aerocat24/aerocat-v2/images/aerocat_with_uav_3.jpg

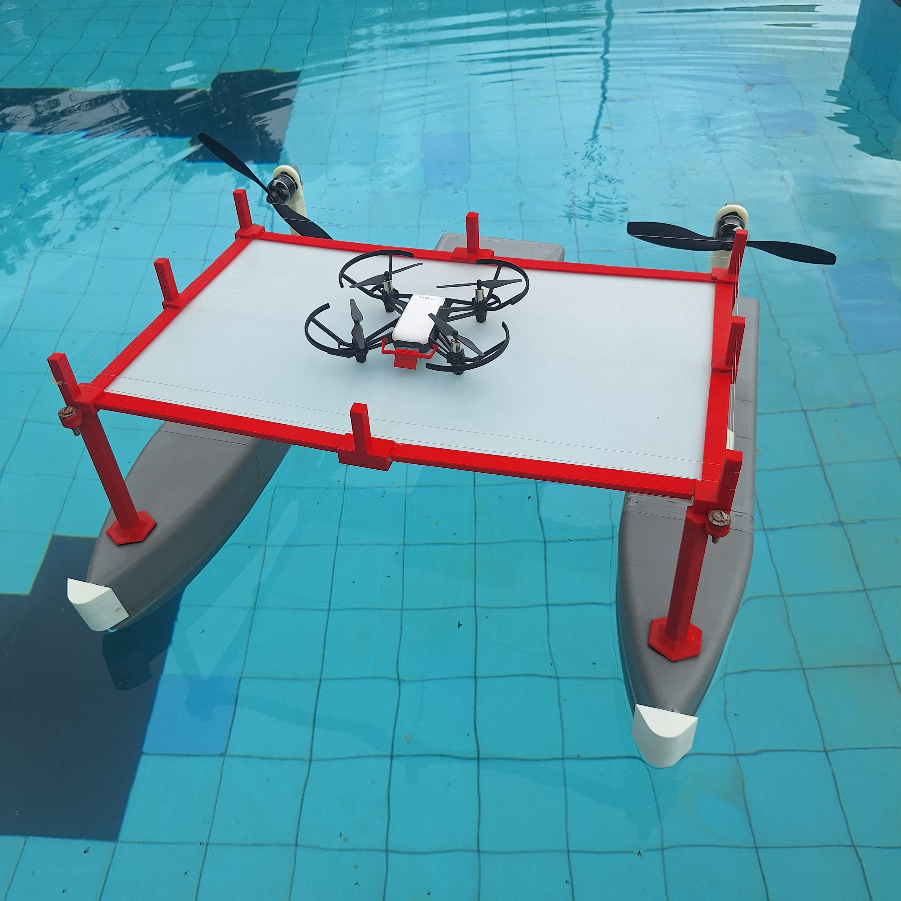
images/aerocat_with_uav_3.jpg
