aerocat24/aerocat-v2/images/aerocat_without_platform_1.jpg

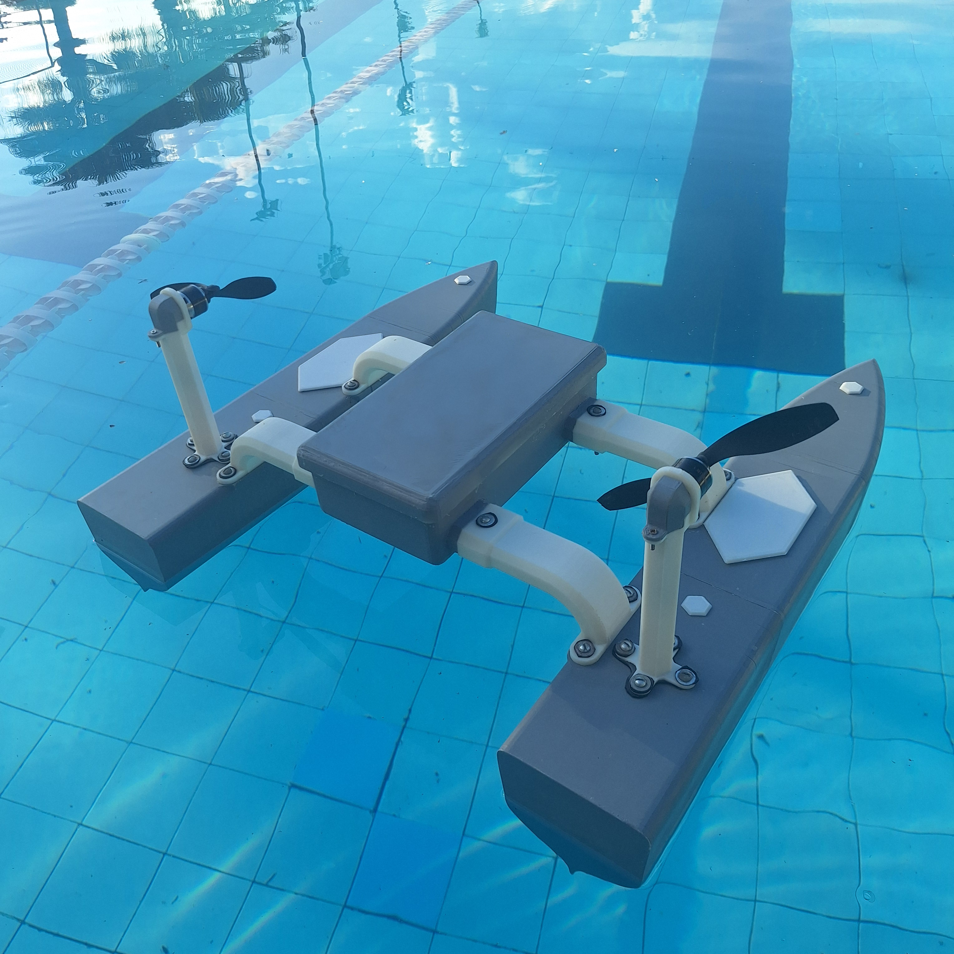
images/aerocat_without_platform_1.jpg
