aerocat24/aerocat-v2/images/aerocat_without_platform_4.jpg

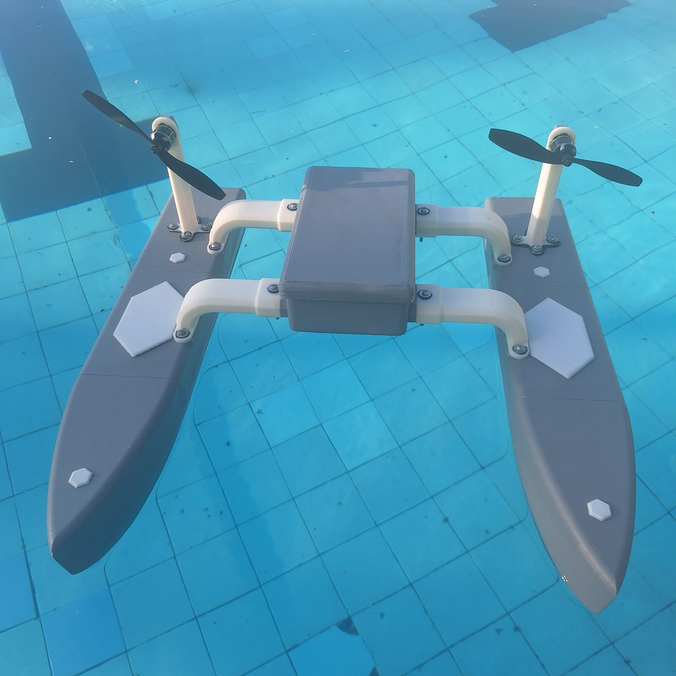
images/aerocat_without_platform_4.jpg
