aerocat24/aerocat-v2/images/mirror_suport.jpg

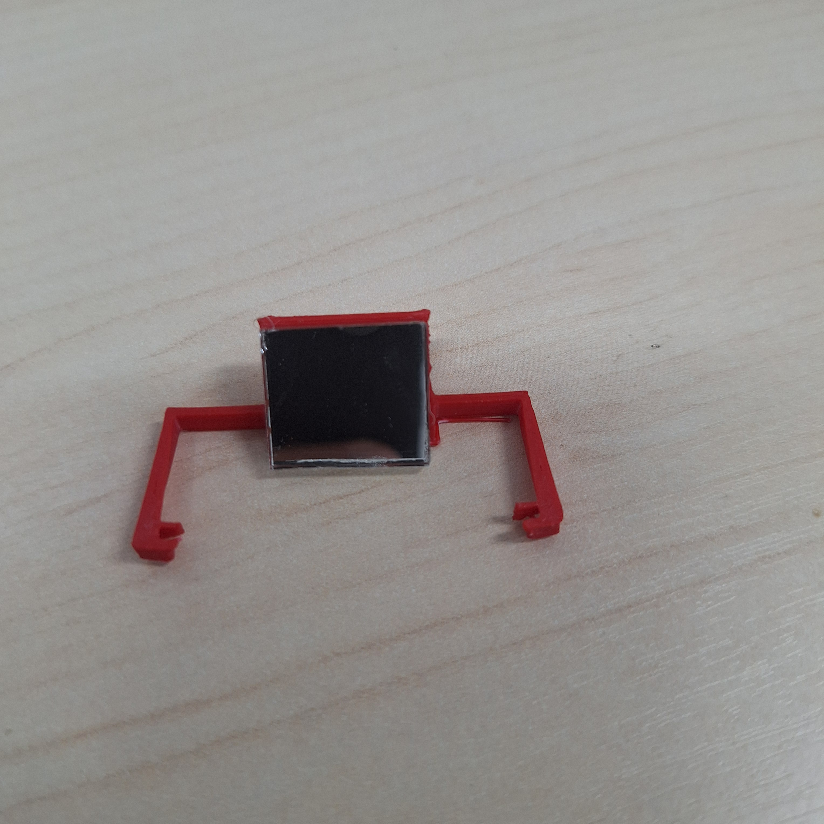
images/mirror_suport.jpg
