aerocat24/aerocat-v2/images/pcb_1.jpg

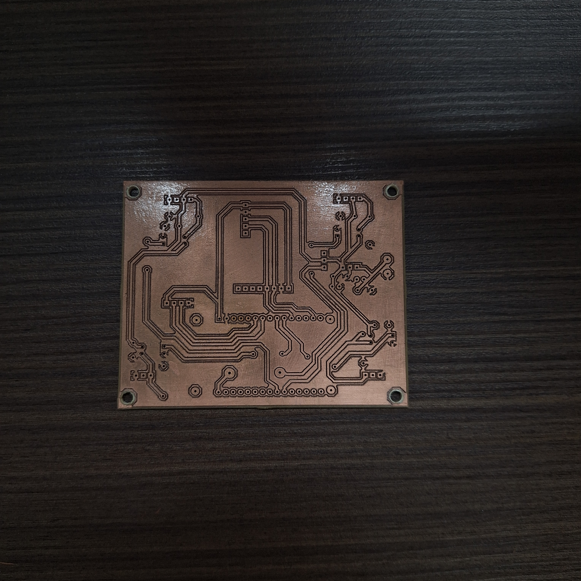
images/pcb_1.jpg
