aerocat24/aerocat-v2/images/uav_dji_tello_1.jpg

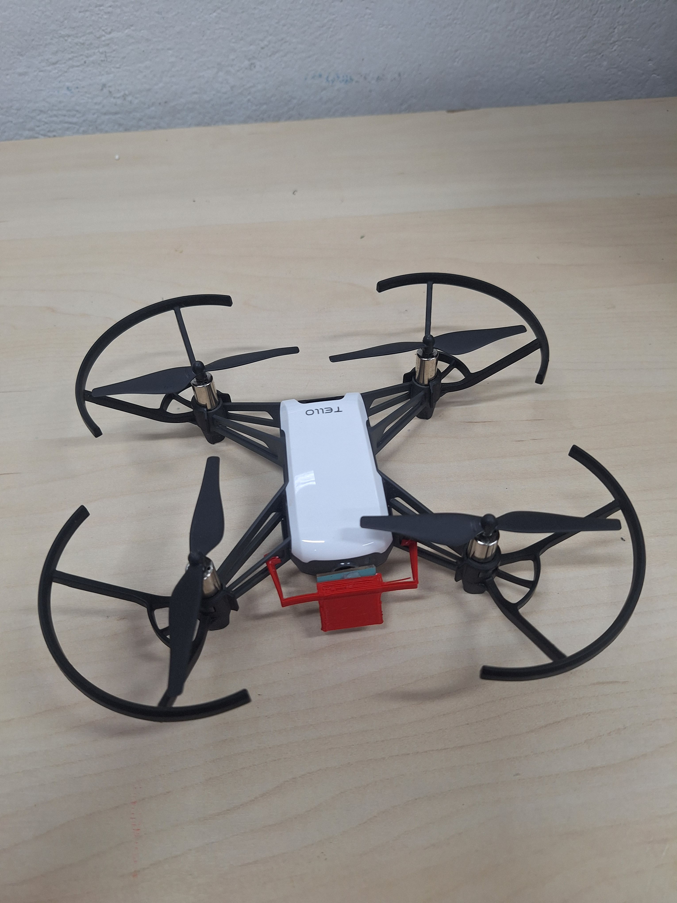
images/uav_dji_tello_1.jpg
