aerocat24/aerocat-v2/images/uav_dji_tello_2.jpg

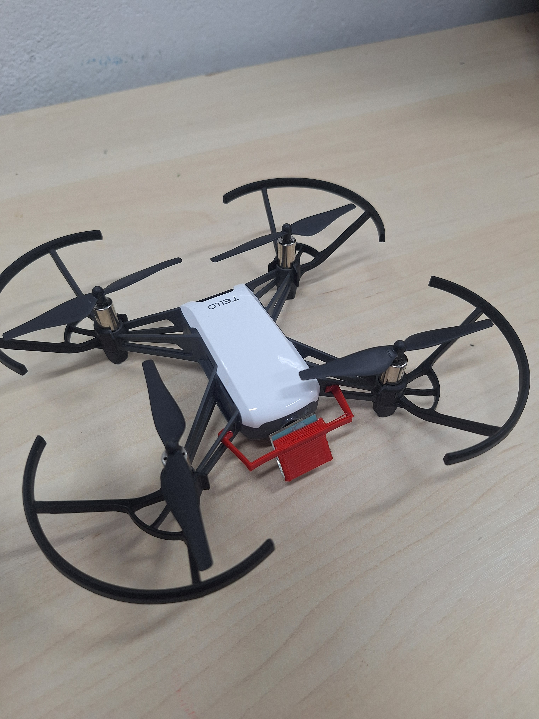
images/uav_dji_tello_2.jpg
