aerocat24/aerocat-v2/PCB/images/pcb_model.png

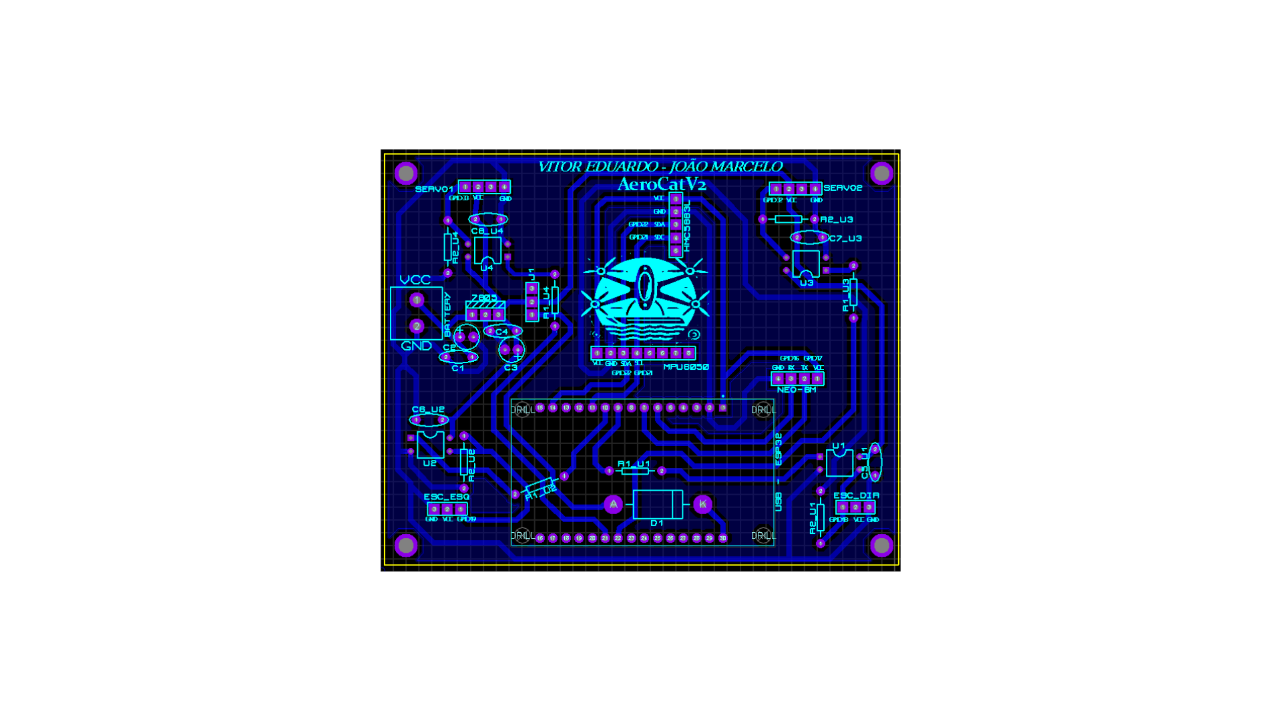
PCB/images/pcb_model.png
