aerocat24/aerocat-v2/PCB/images/Routes.jpg

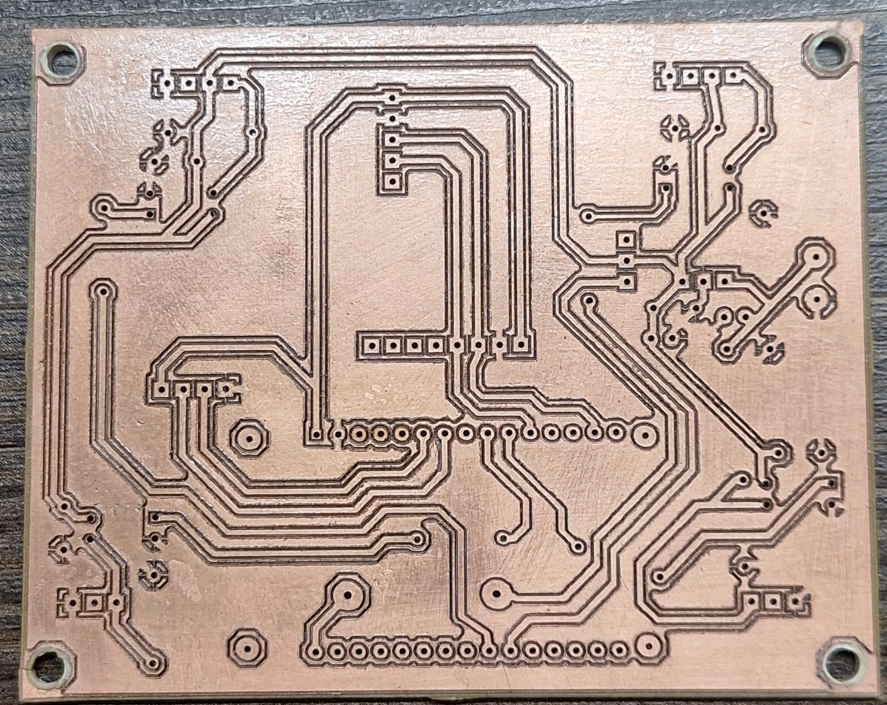
PCB/images/Routes.jpg
