aerocat24/aerocat-v2/STL/images/01_front_hull.png

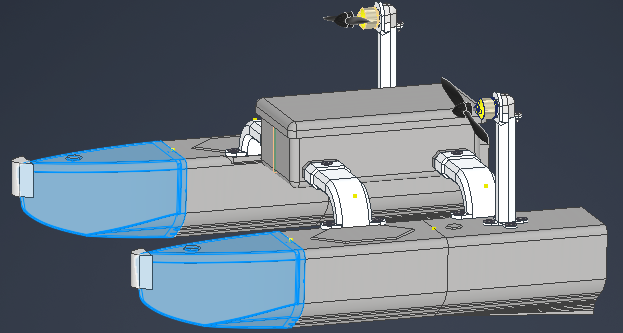
STL/images/01_front_hull.png
