aerocat24/aerocat-v2/STL/images/02_right_middle_hull.png

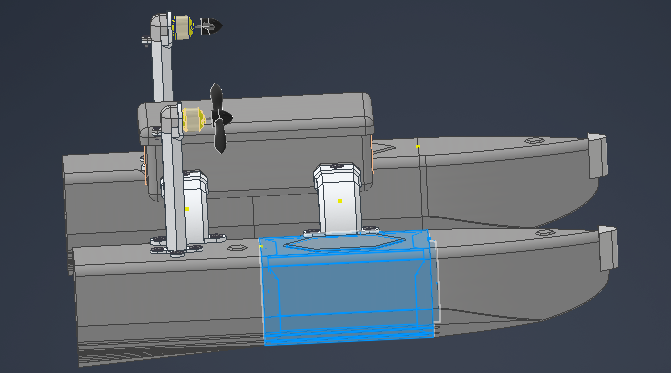
STL/images/02_right_middle_hull.png
