aerocat24/aerocat-v2/STL/images/03_left_middle_hull.png

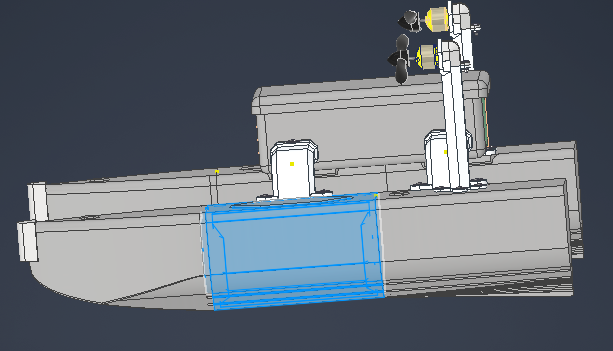
STL/images/03_left_middle_hull.png
