aerocat24/aerocat-v2/STL/images/04_right_rear_hull.png

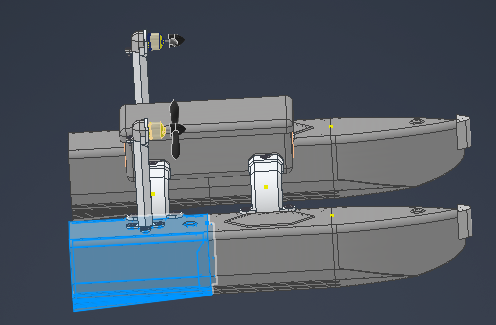
STL/images/04_right_rear_hull.png
