aerocat24/aerocat-v2/STL/images/05_left_rear_hull.png

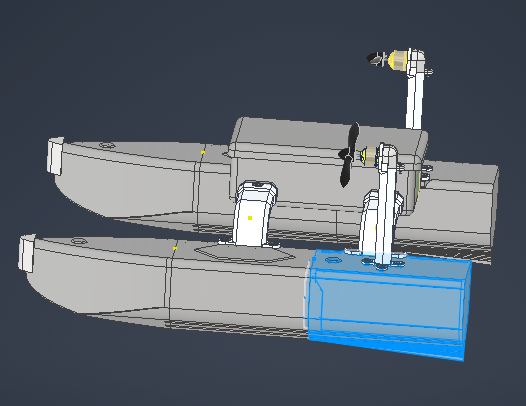
STL/images/05_left_rear_hull.png
