aerocat24/aerocat-v2/STL/images/06_small_hull_cover.png

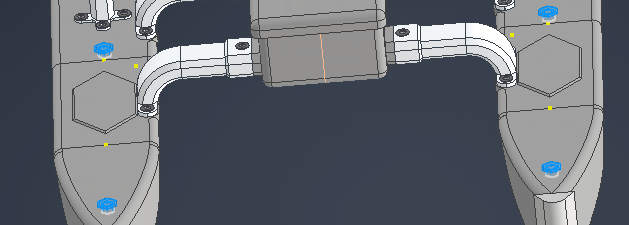
STL/images/06_small_hull_cover.png
