aerocat24/aerocat-v2/STL/images/07_large_hull_cover.png

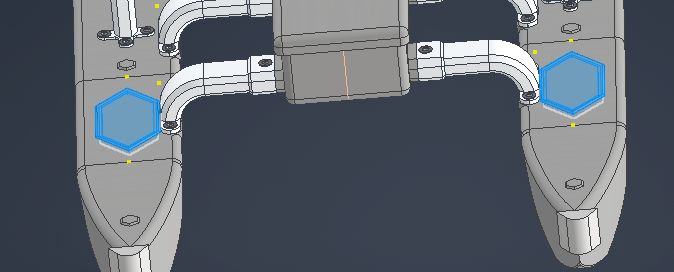
STL/images/07_large_hull_cover.png
