aerocat24/aerocat-v2/STL/images/08_module_hull_handle.png

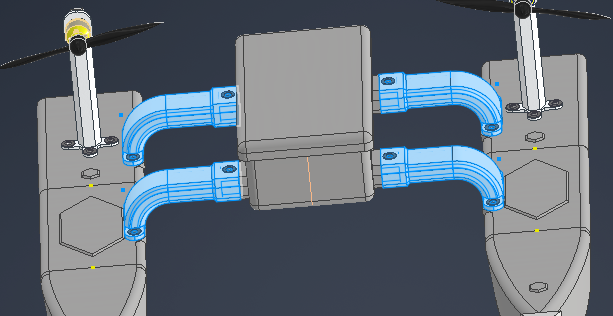
STL/images/08_module_hull_handle.png
