aerocat24/aerocat-v2/STL/images/09_motor_base.png

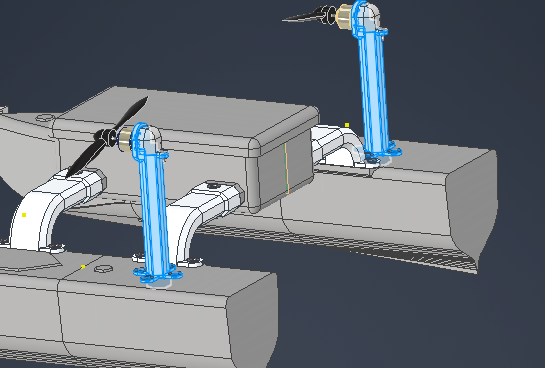
STL/images/09_motor_base.png
