aerocat24/aerocat-v2/STL/images/10_motor_base_cover.png

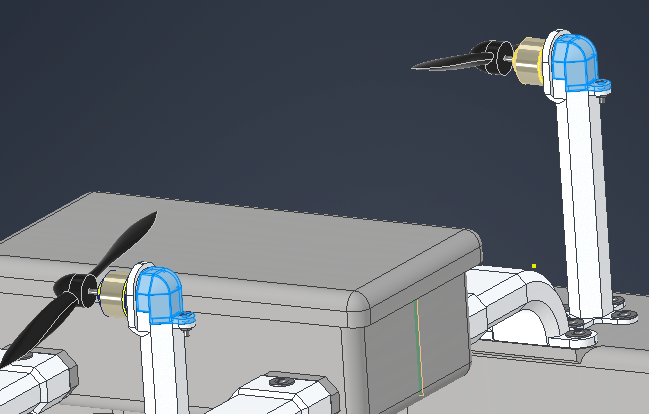
STL/images/10_motor_base_cover.png
