aerocat24/aerocat-v2/STL/images/11_module.png

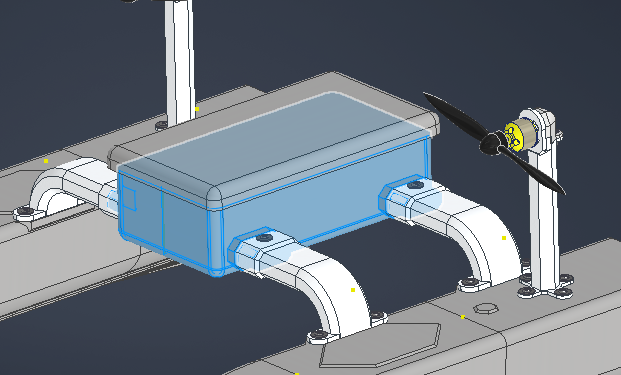
STL/images/11_module.png
