aerocat24/aerocat-v2/STL/images/12_module_cover.png

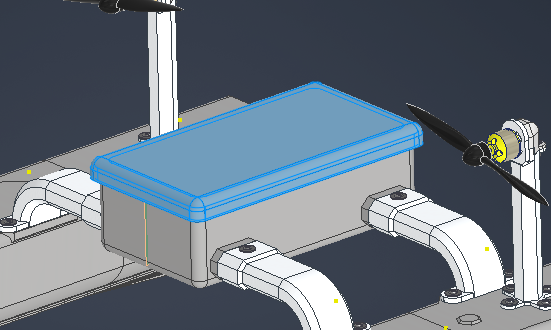
STL/images/12_module_cover.png
