aerocat24/aerocat-v2/STL/images/13_front_hull_guard.png

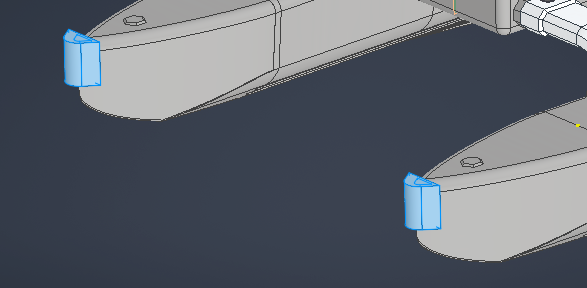
STL/images/13_front_hull_guard.png
