aerocat24/aerocat-v2/STL/images/14_front_platform_base.png

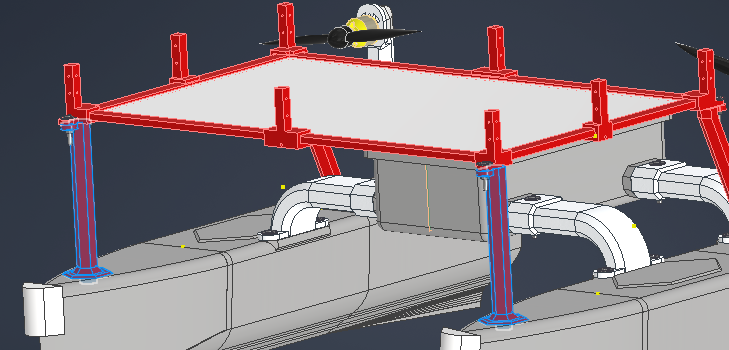
STL/images/14_front_platform_base.png
