aerocat24/aerocat-v2/STL/images/15_rear_platform_base.png

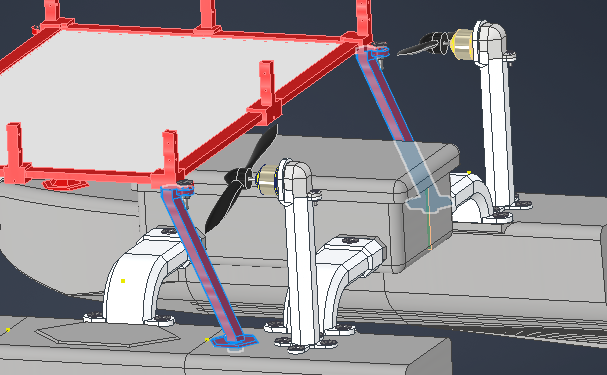
STL/images/15_rear_platform_base.png
