aerocat24/aerocat-v2/STL/images/16_large_platform_channel.png

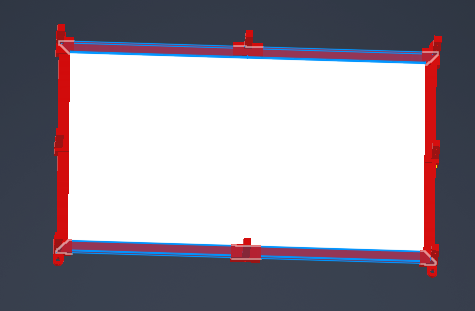
STL/images/16_large_platform_channel.png
