aerocat24/aerocat-v2/STL/images/17_small_platform_channel.png

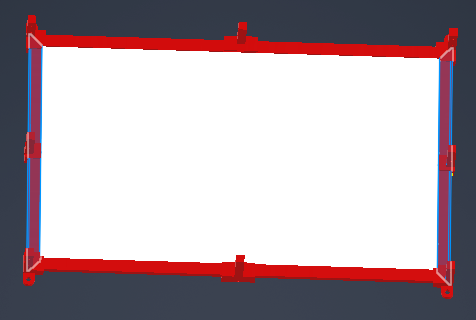
STL/images/17_small_platform_channel.png
