aerocat24/aerocat-v2/STL/images/19_platform_base_diagonal_channel_support_1.png

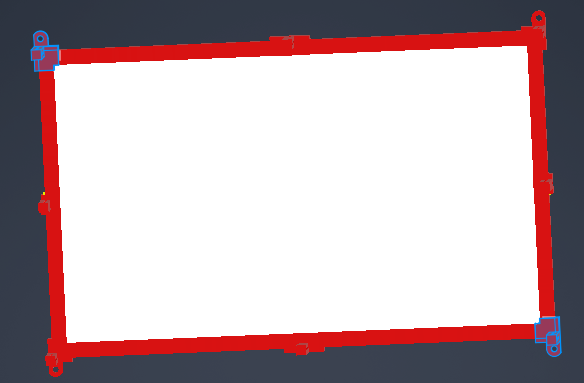
STL/images/19_platform_base_diagonal_channel_support_1.png
