aerocat24/aerocat-v2/STL/images/20_platform_base_diagonal_channel_support_2.png

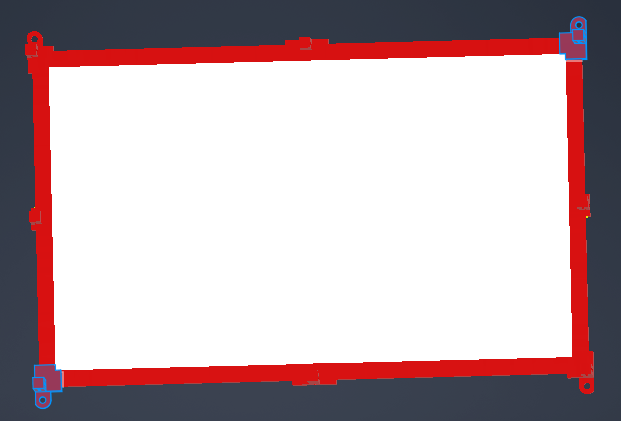
STL/images/20_platform_base_diagonal_channel_support_2.png
