aerocat24/aerocat-v2/STL/images/22_platform_center_support.png

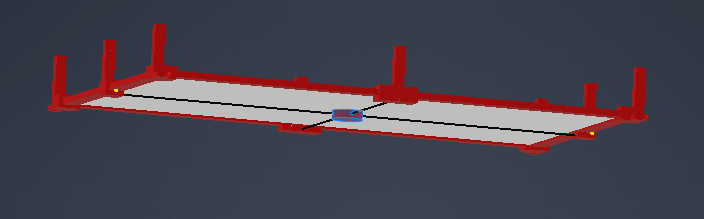
STL/images/22_platform_center_support.png
