aerocat24/aerocat-v2/STL/14_front_platform_base.stl

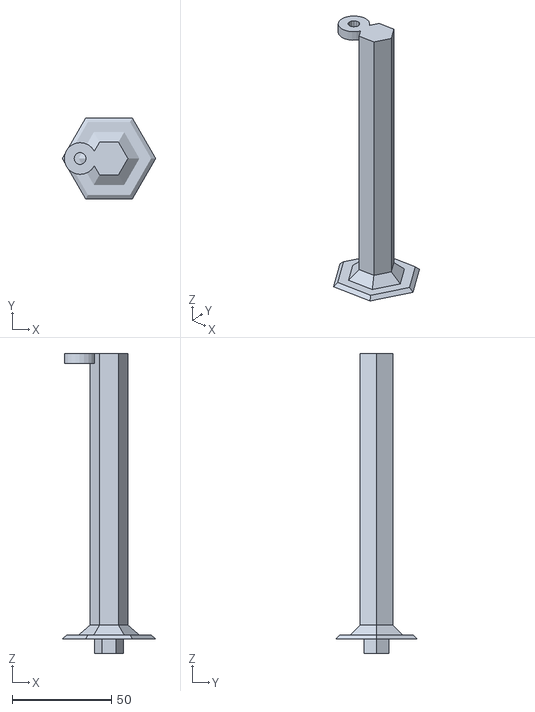
[picture p81: CAD file, 2026-05-18]
STL/14_front_platform_base.stl
47.0 x 40.7 x 150.8
