aerocat24/aerocat-v2/ROS/boat_drone_ws/src/hector_quadrotor_noetic/hector_gazebo/hector_gazebo_worlds/Media/models/drc_qual4_block.stl

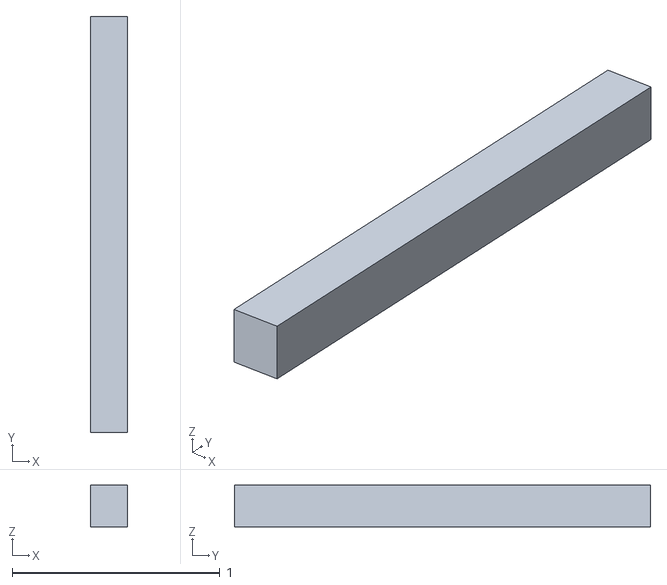
[picture p82: CAD file, 2026-05-22]
ROS/boat_drone_ws/src/hector_quadrotor_noetic/hector_gazebo/hector_gazebo_worlds/Media/models/drc_qual4_block.stl
0.18 x 2.00 x 0.2
