aerocat24/aerocat-v2/STL/16_large_platform_channel.stl

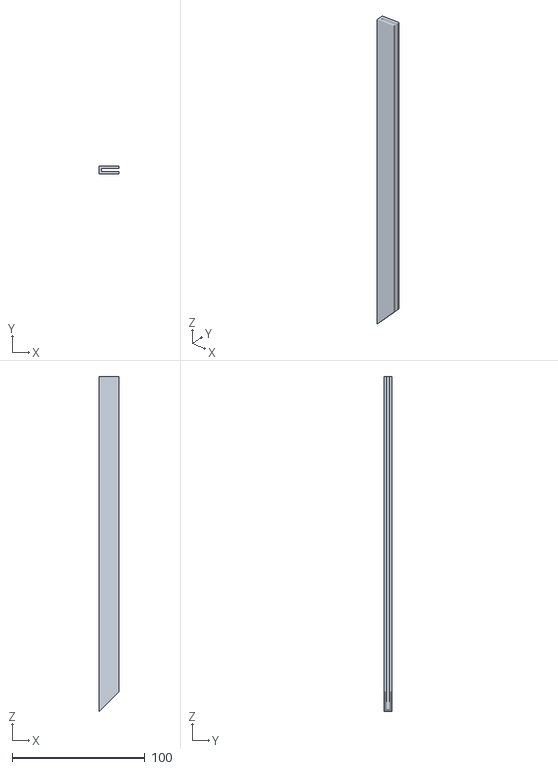
[picture p83: CAD file, 2026-05-18]
STL/16_large_platform_channel.stl
15.0 x 6.20 x 252.0
