aerocat24/aerocat-v2/ROS/boat_drone_ws/src/hector_quadrotor_noetic/hector_gazebo/hector_gazebo_worlds/Media/models/sick_robot_day_2014_ring.stl

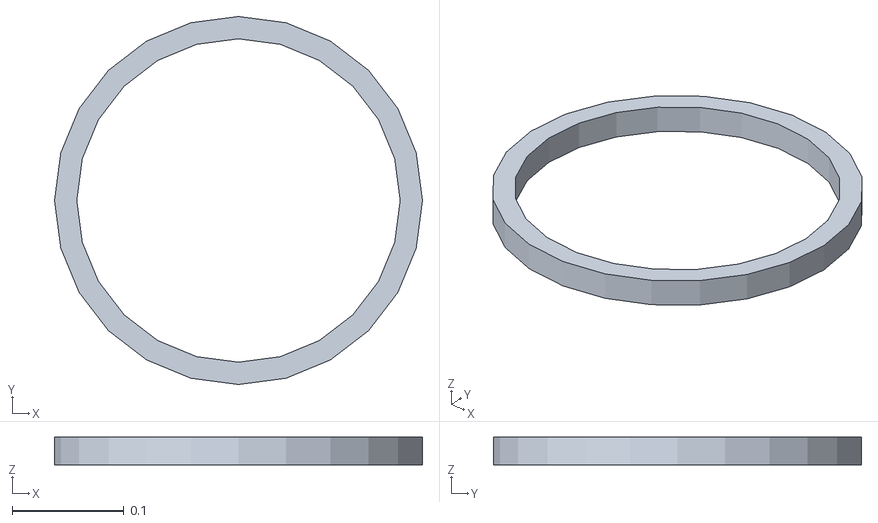
[picture p84: CAD file, 2026-05-22]
ROS/boat_drone_ws/src/hector_quadrotor_noetic/hector_gazebo/hector_gazebo_worlds/Media/models/sick_robot_day_2014_ring.stl
0.33 x 0.33 x 0.025
