aerocat24/aerocat-v2/STL/01_front_hull.stl

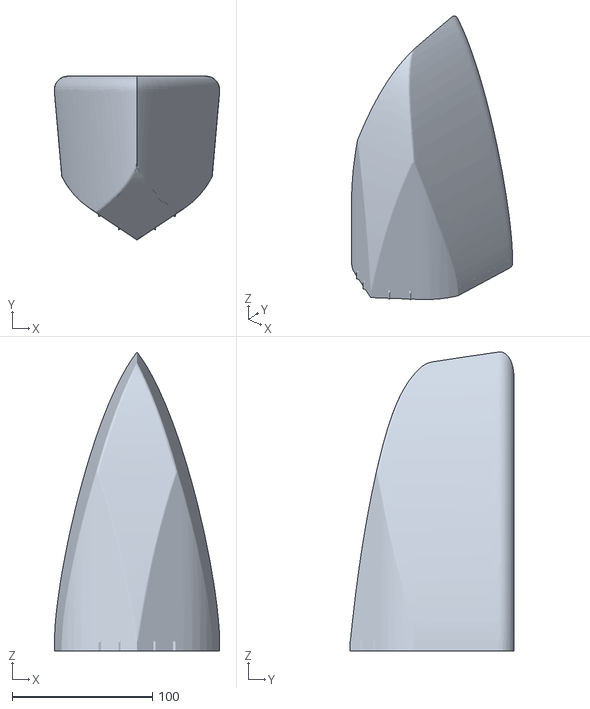
[picture p85: CAD file, 2026-05-18]
STL/01_front_hull.stl
118.1 x 117.0 x 213.5
