aerocat24/aerocat-v2/STL/08_module_hull_handle.stl

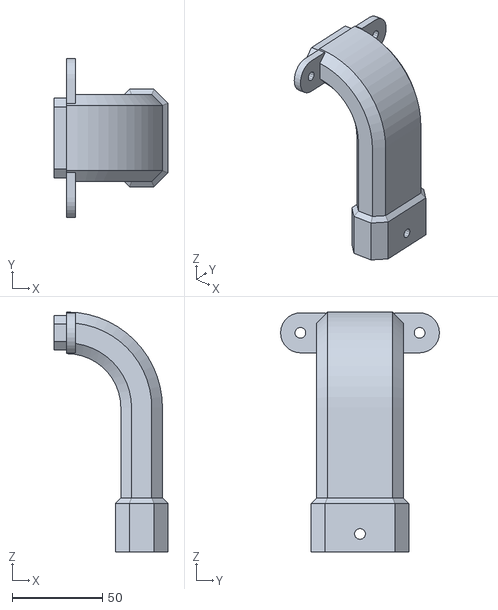
[picture p86: CAD file, 2026-05-18]
STL/08_module_hull_handle.stl
63.1 x 88.1 x 133.1
