aerocat24/aerocat-v2/STL/11_module.stl

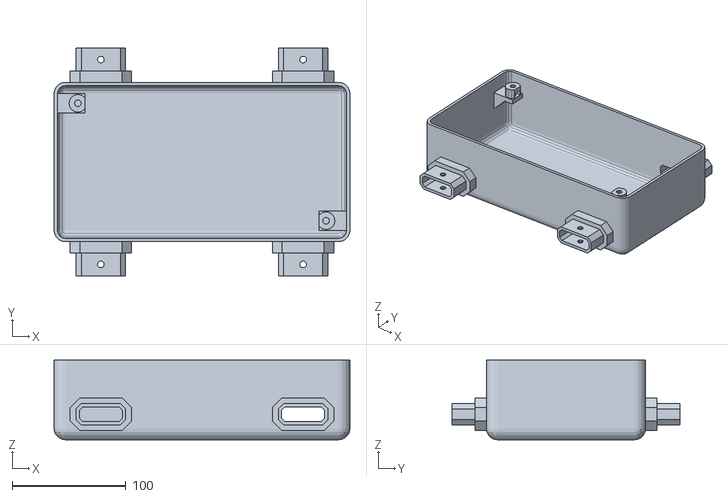
[picture p87: CAD file, 2026-05-18]
STL/11_module.stl
260.0 x 200.0 x 70.0
