aerocat24/aerocat-v2/STL/19_platform_base_diagonal_channel_support_1.stl

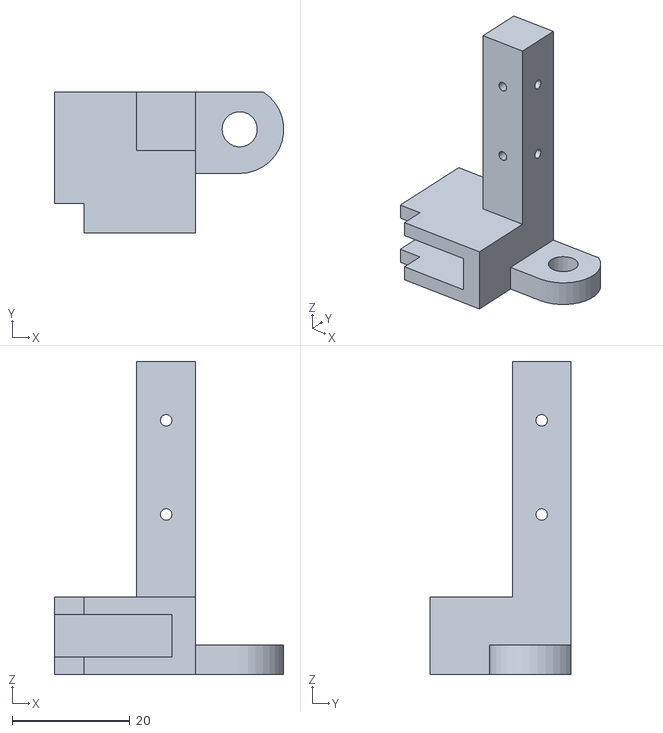
[picture p88: CAD file, 2026-05-18]
STL/19_platform_base_diagonal_channel_support_1.stl
39.0 x 24.0 x 53.2
