aerocat24/aerocat-v2/STL/15_rear_platform_base.stl

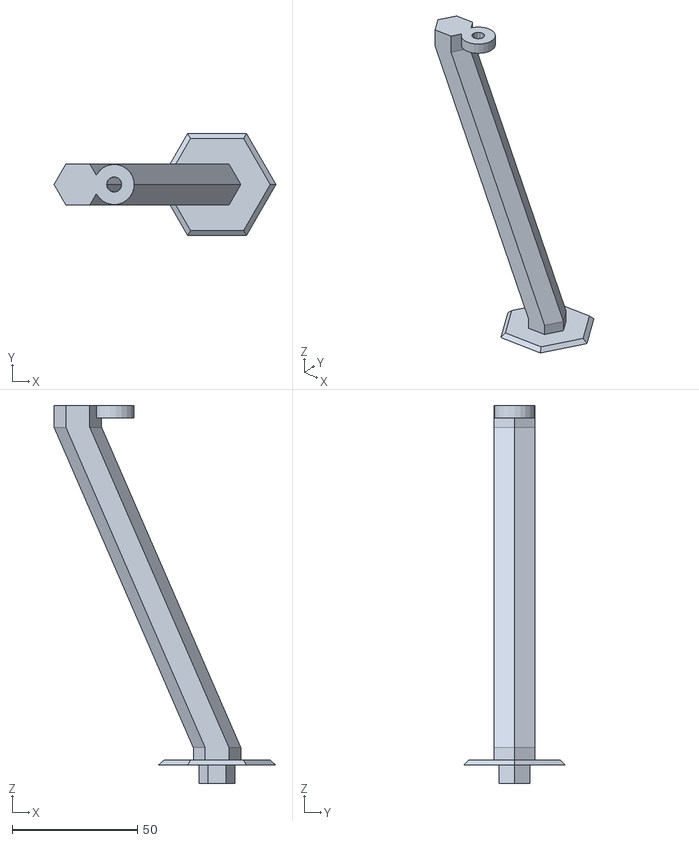
[picture p89: CAD file, 2026-05-18]
STL/15_rear_platform_base.stl
88.5 x 40.7 x 150.8
