aerocat24/aerocat-v2/STL/04_right_rear_hull.stl

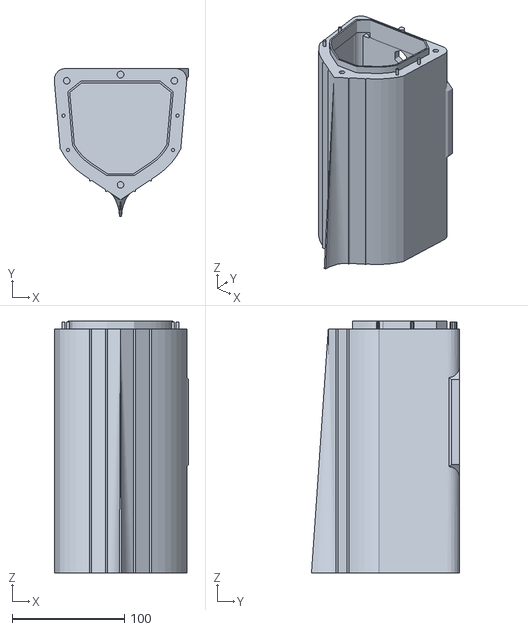
[picture p90: CAD file, 2026-05-18]
STL/04_right_rear_hull.stl
119.8 x 132.0 x 224.6
