aerocat24/aerocat-v2/STL/06_small_hull_cover.stl

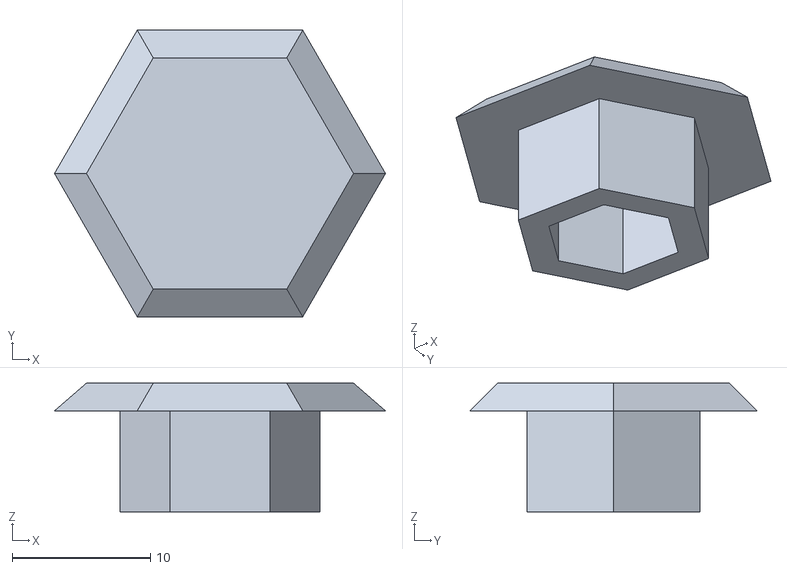
[picture p91: CAD file, 2026-05-18]
STL/06_small_hull_cover.stl
23.9 x 20.7 x 9.30
