aerocat24/aerocat-v2/STL/09_motor_base.stl

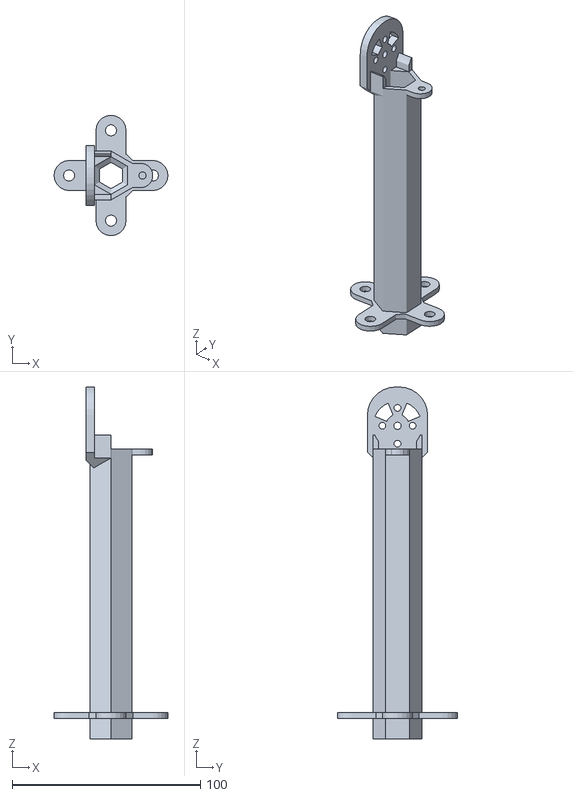
[picture p92: CAD file, 2026-05-18]
STL/09_motor_base.stl
60.5 x 64.0 x 187.0
