aerocat24/aerocat-v2/STL/12_module_cover.stl

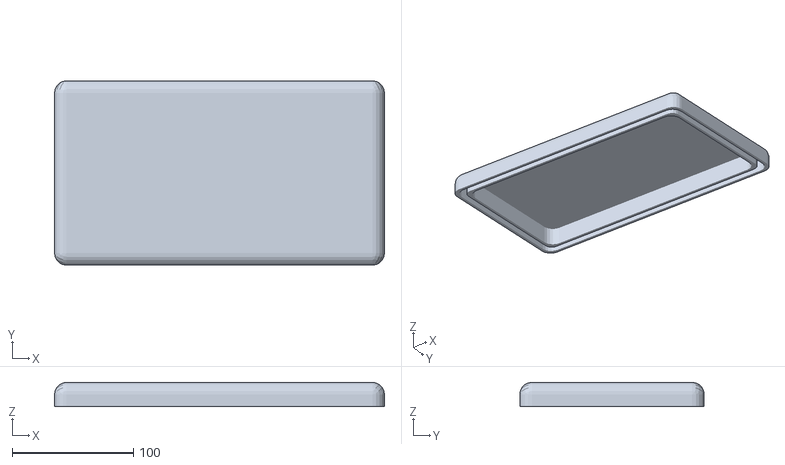
[picture p93: CAD file, 2026-05-18]
STL/12_module_cover.stl
272.0 x 152.0 x 20.0
