aerocat24/aerocat-v2/STL/13_front_hull_guard.stl

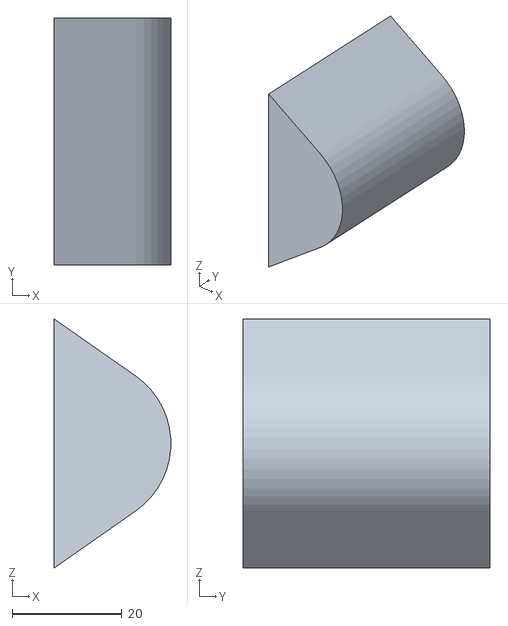
[picture p94: CAD file, 2026-05-18]
STL/13_front_hull_guard.stl
21.3 x 45.0 x 45.4
