aerocat24/aerocat-v2/STL/07_large_hull_cover.stl

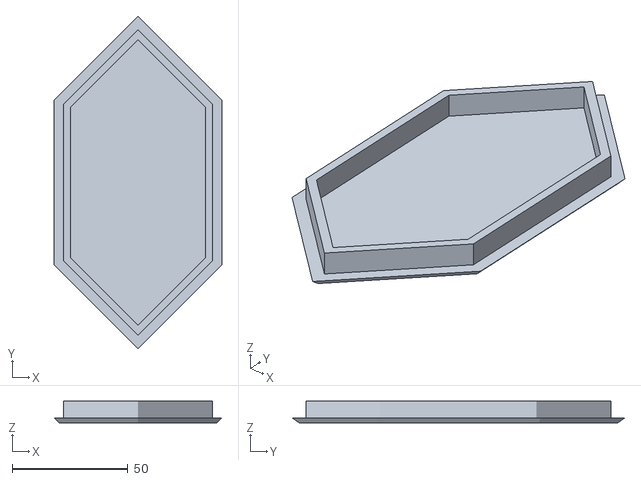
[picture p95: CAD file, 2026-05-18]
STL/07_large_hull_cover.stl
72.5 x 143.5 x 9.30
