aerocat24/aerocat-v2/STL/18_large_platform_channel_support.stl

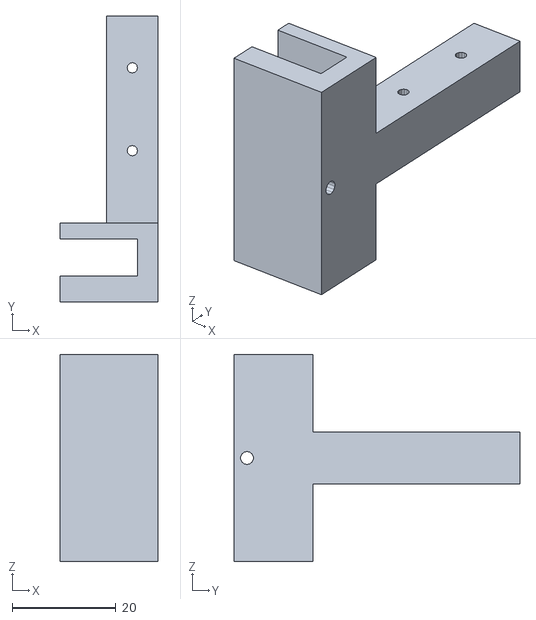
[picture p96: CAD file, 2026-05-18]
STL/18_large_platform_channel_support.stl
19.0 x 55.2 x 40.0
