aerocat24/aerocat-v2/STL/17_small_platform_channel.stl

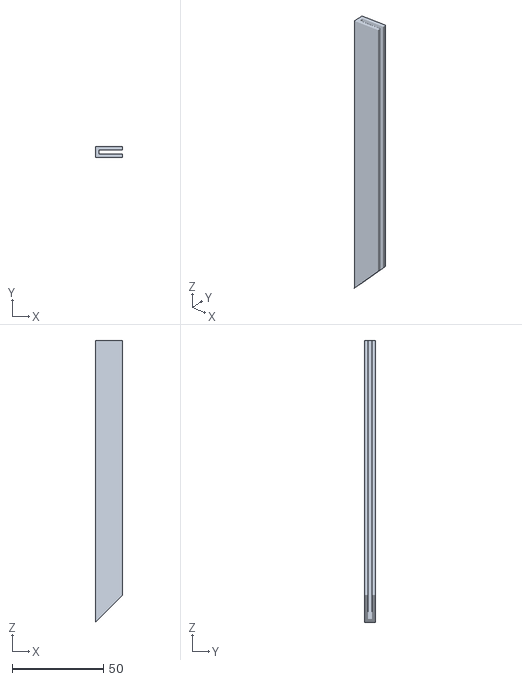
[picture p97: CAD file, 2026-05-18]
STL/17_small_platform_channel.stl
15.0 x 6.20 x 154.2
