aerocat24/aerocat-v2/STL/22_platform_center_support.stl

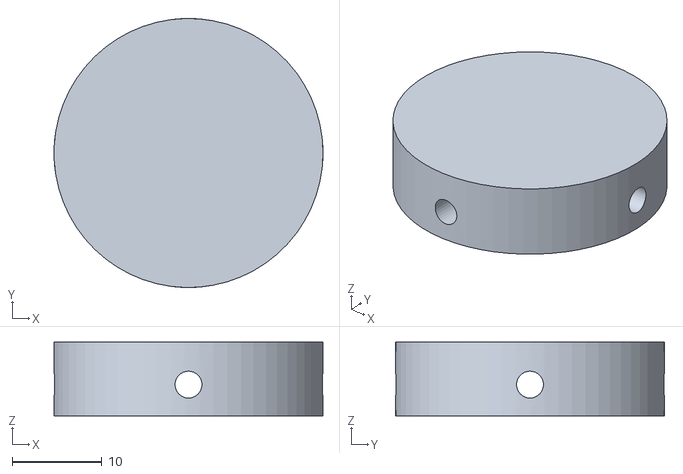
[picture p98: CAD file, 2026-05-18]
STL/22_platform_center_support.stl
30.0 x 30.0 x 8.25
