aerocat24/aerocat-v2/STL/21_small_platform_channel_support.stl

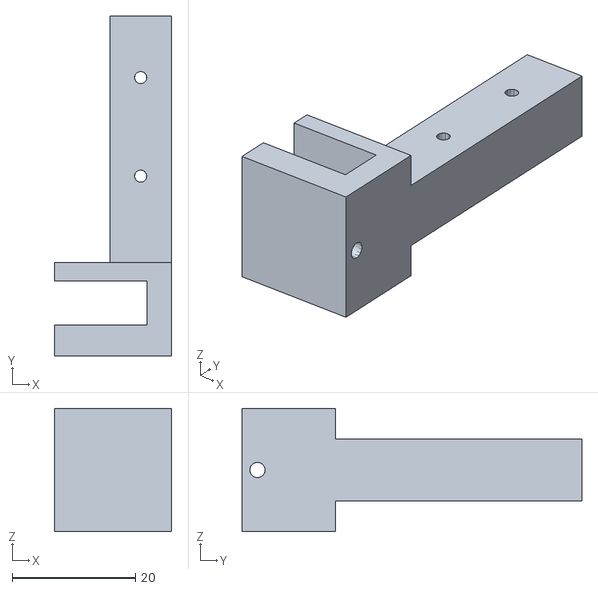
[picture p99: CAD file, 2026-05-18]
STL/21_small_platform_channel_support.stl
19.0 x 55.2 x 20.0
