aerocat24/aerocat-v2/images/assembled PCB_3.jpg

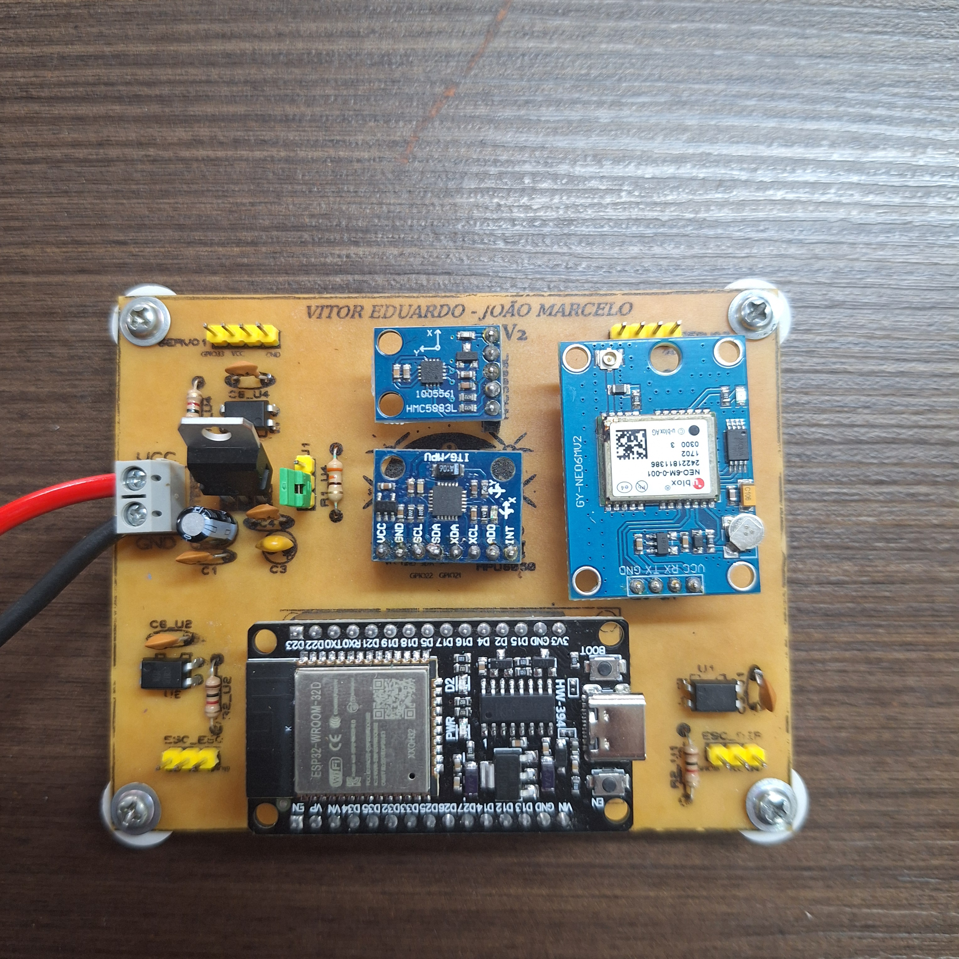
images/assembled PCB_3.jpg
