aerocat24/aerocat-v2/PCB/images/assembled PCB_1.jpg

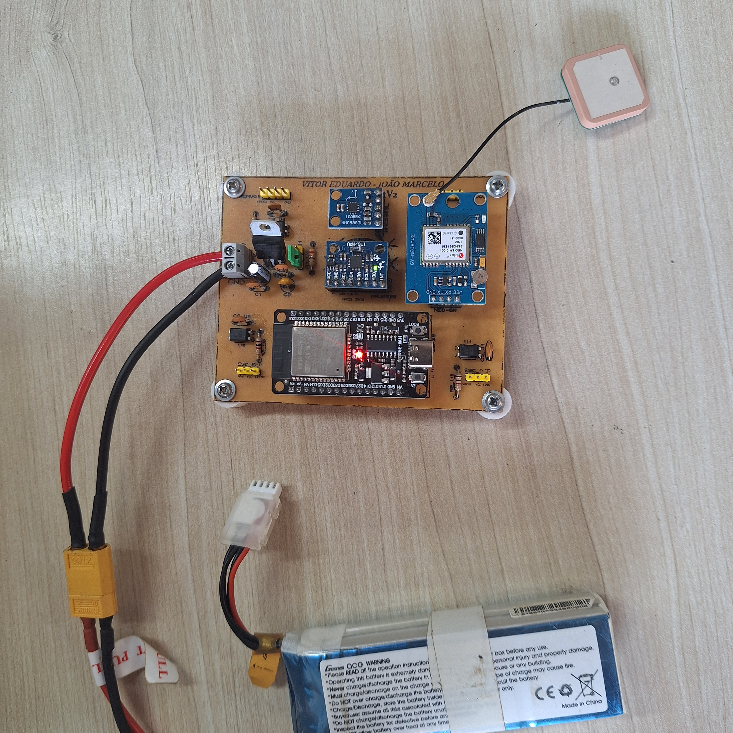
PCB/images/assembled PCB_1.jpg
