aerocat24/aerocat-v2/images/aerocat_with_platform_1.jpg

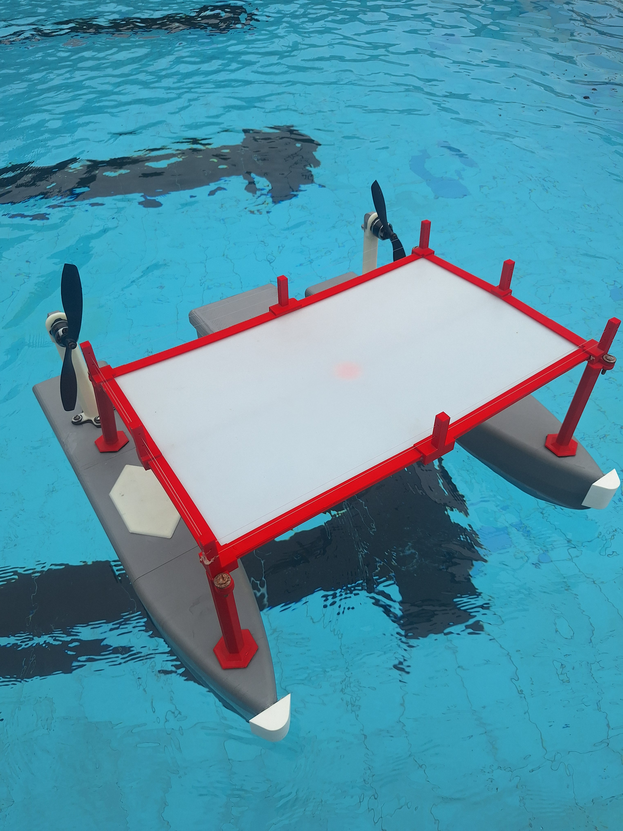
images/aerocat_with_platform_1.jpg
