aerocat24/aerocat-v2/images/aerocat_with_platform_3.jpg

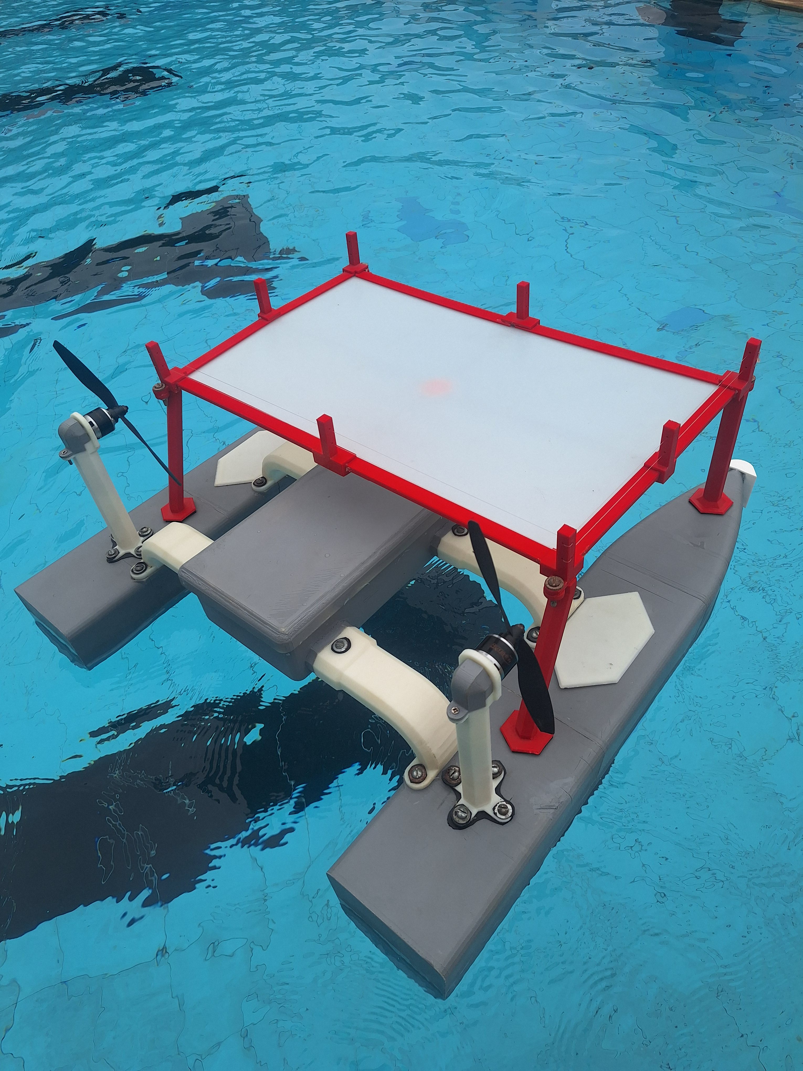
images/aerocat_with_platform_3.jpg
