aerocat24/aerocat-v2/images/aerocat_with_platform_4.jpg

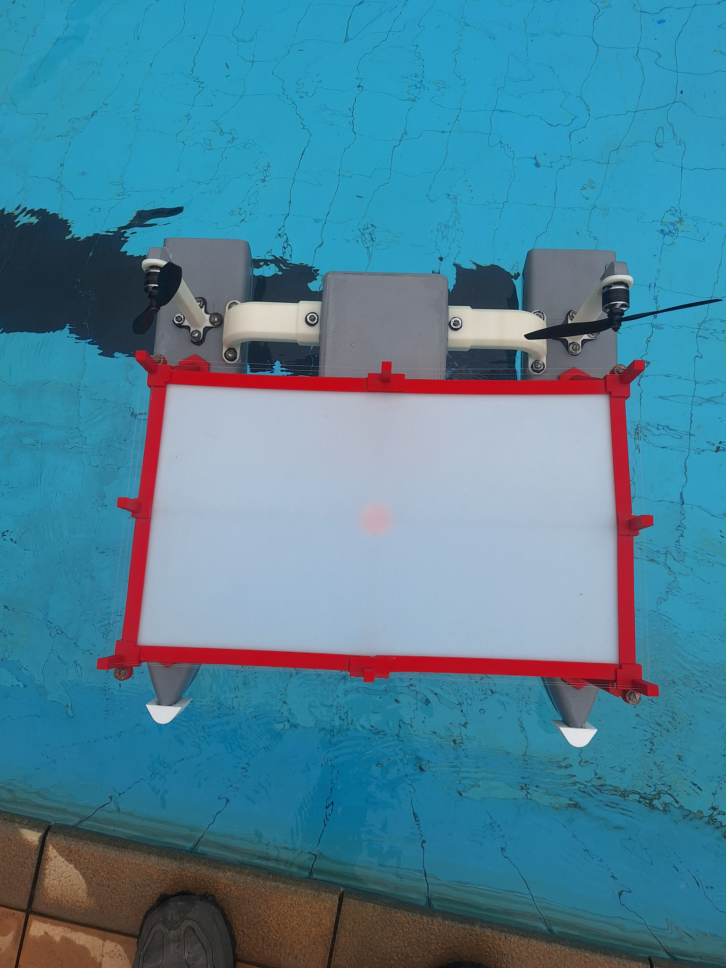
images/aerocat_with_platform_4.jpg
